lhp1507/diploma-project/source-code/Server/note.docx

1. Thư mục Server chứa mã nguồn xử lý ở server.
2. Thư mục templates bên trong thư mục Server chứa trang web và mã nguồn xử lý PHP.

SVTH: Trần Thế Đẩu, Lê Hữu Phú, Nguyễn Ngọc Quang GVHD: ThS. Hồ Viết Việt

Hệ thống nhắc nhở uống thuốc dựa trên nền tảng IoT
