lhp1507/diploma-project/data/diagrams/flowchart/hour.PNG

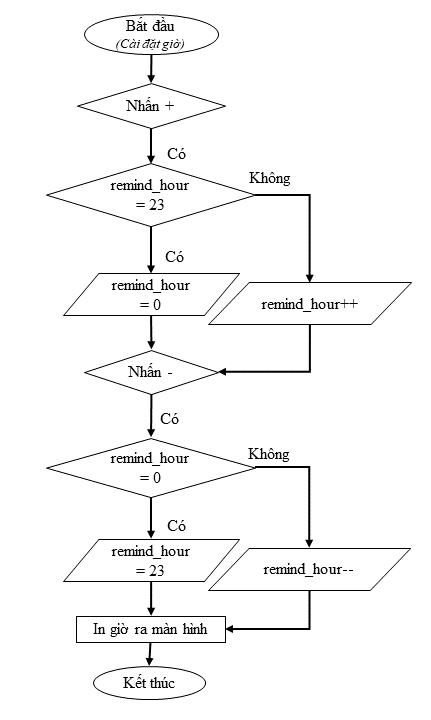
data/diagrams/flowchart/hour.PNG
