lhp1507/diploma-project/pcb/altium/machESP32/final/3d.png

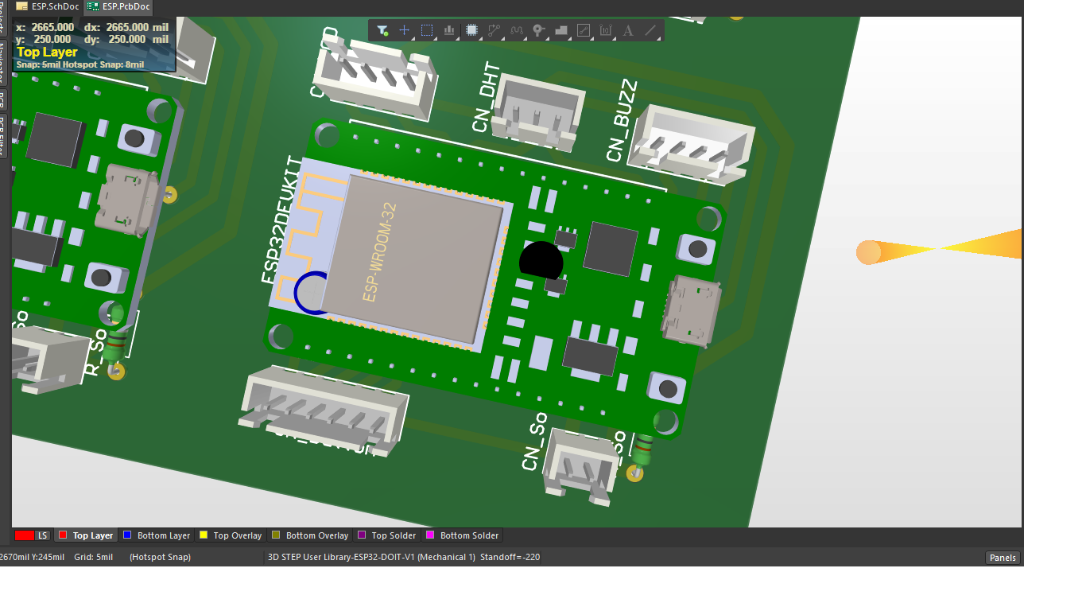
pcb/altium/machESP32/final/3d.png
