lhp1507/diploma-project/pcb/altium/machESP32/final/sche.png

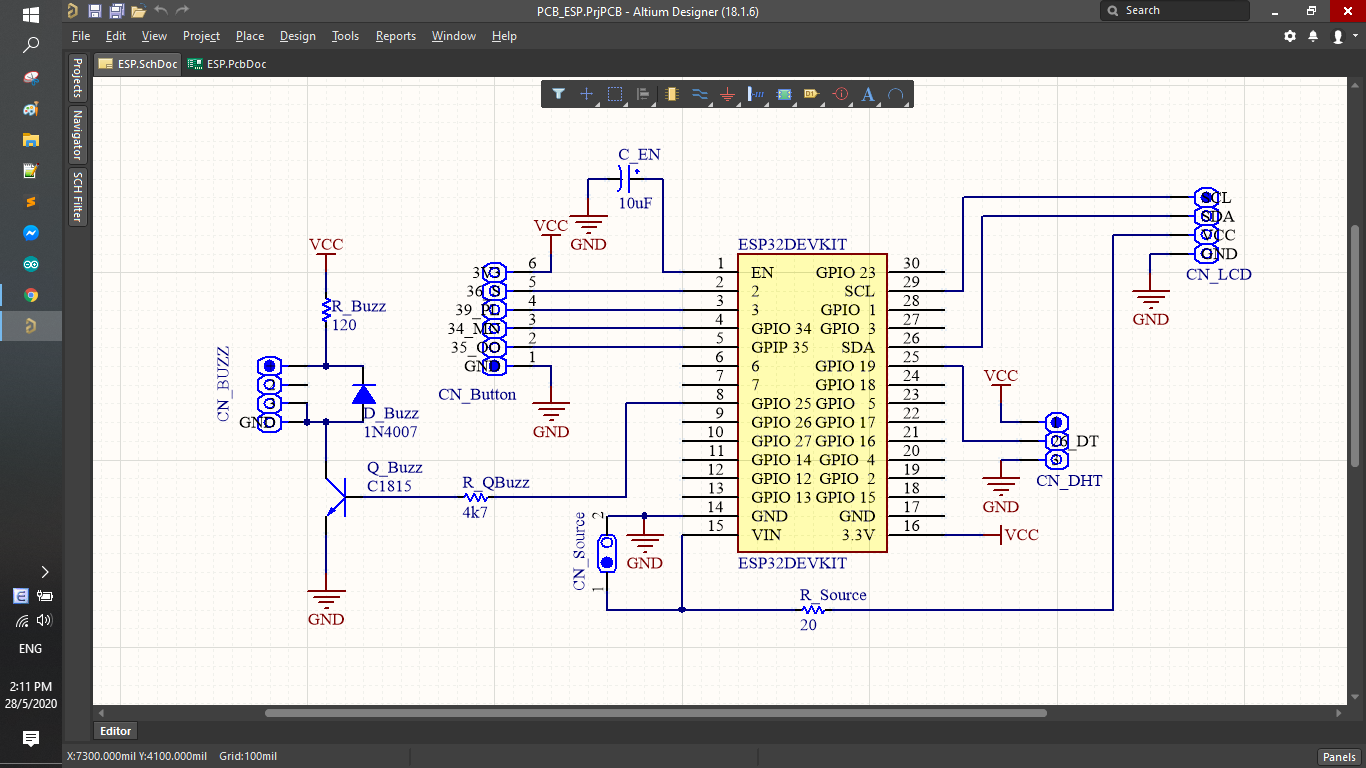
pcb/altium/machESP32/final/sche.png
