lhp1507/diploma-project/pcb/altium/machESP32/final/wire.png

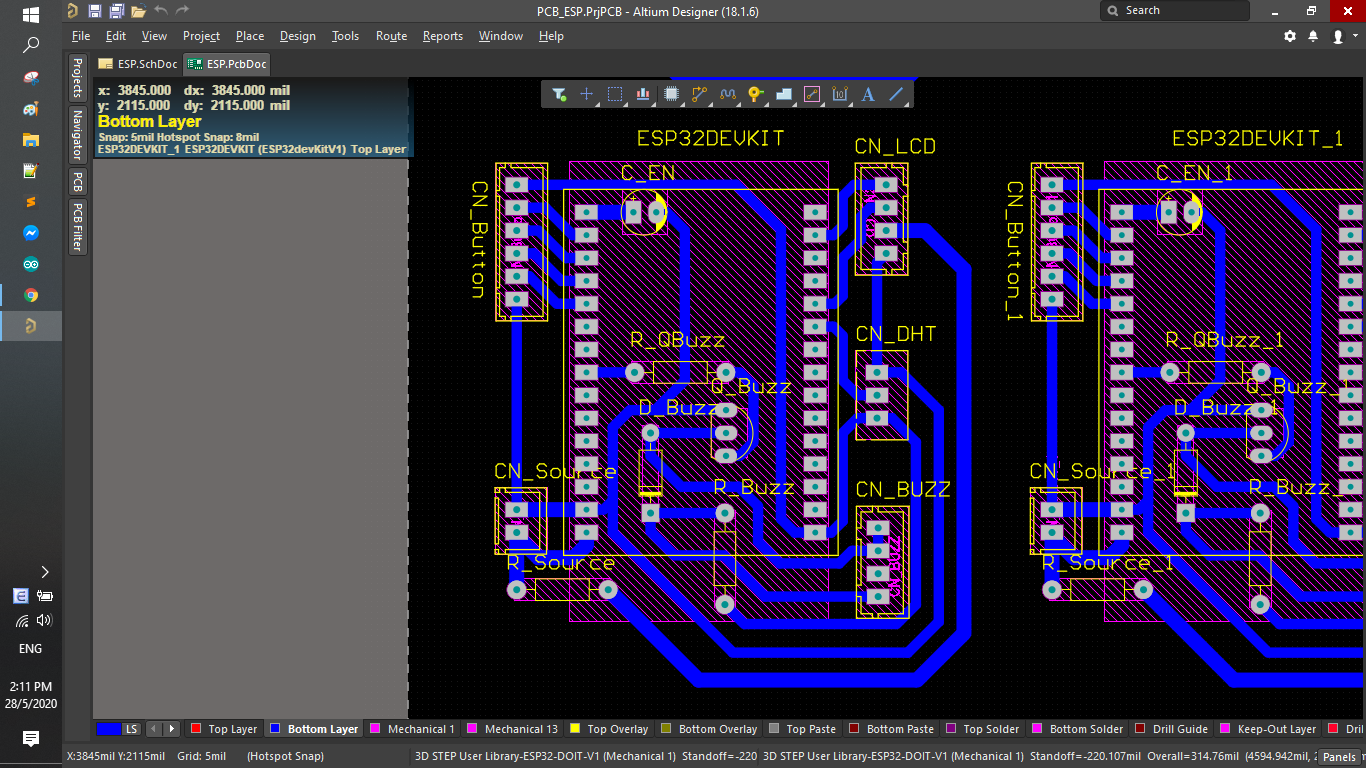
pcb/altium/machESP32/final/wire.png
