lhp1507/diploma-project/source-code/Server/templates/img/NguyenNgocQuang(QuangNN13).jpg

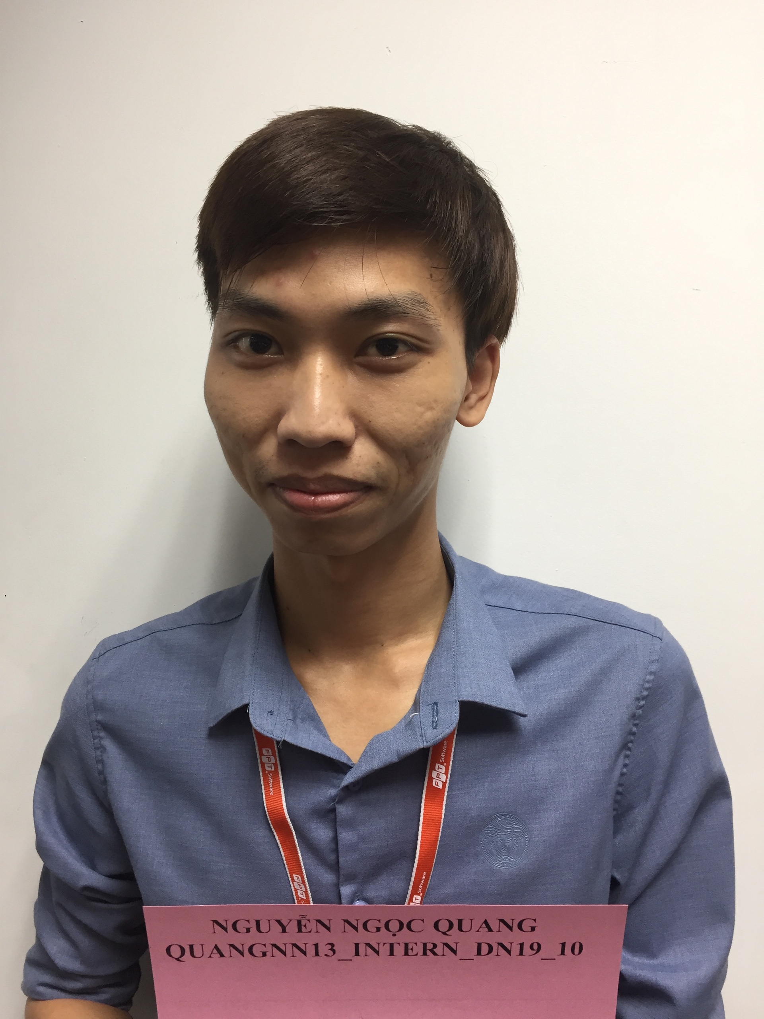
source-code/Server/templates/img/NguyenNgocQuang(QuangNN13).jpg
