lhp1507/diploma-project/source-code/Server/templates/img/TranTheDau(dautt).jpg

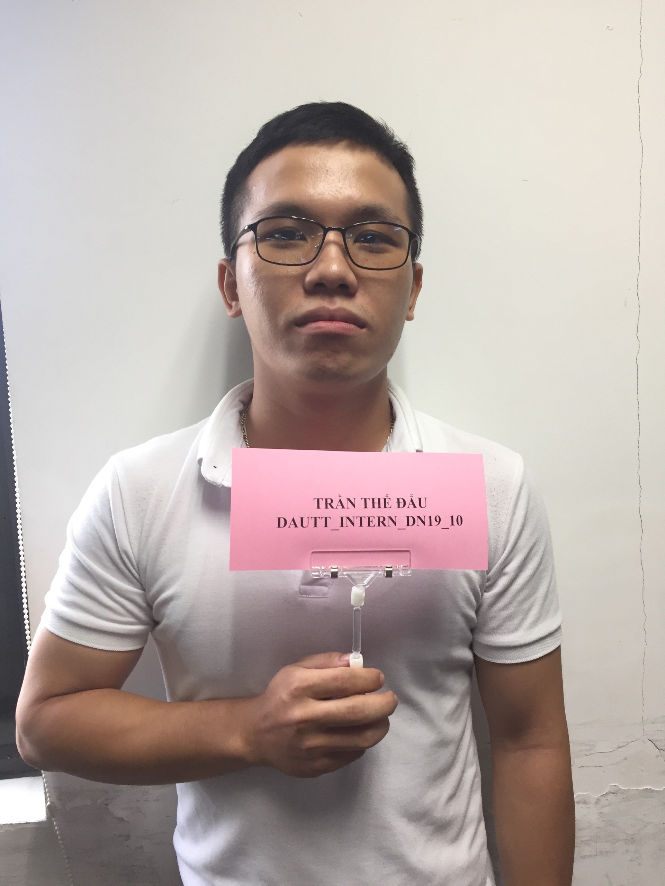
source-code/Server/templates/img/TranTheDau(dautt).jpg
